NUBIVlab/SpiderCam/fpga/tb/components/drivers/FpDriver32.sv

import utilities_pkg::*;

class FpDriver32 #(type T, type I);

    TriggerableQueue #(T) in_queue;
    I inf;

    function new(
        TriggerableQueue #(T) in_queue,
        I inf
    );
        this.in_queue = in_queue;
        this.inf = inf;
    endfunction

    task automatic drive_fp(T floating_points);
        inf.fp_a_i  <= floating_points.a;
        inf.fp_b_i  <= floating_points.b;
        inf.valid_i <= 1;
        @(posedge this.inf.clk_i);
    endtask;

    task automatic invalidate();
        inf.valid_i <= 0;
    endtask;

    task automatic run();
        T floating_points;
        invalidate();

        forever begin
            in_queue.pop(floating_points);
            drive_fp(floating_points);
            invalidate();
        end
    endtask
endclass
