NUBIVlab/SpiderCam/fpga/projects/dfdd/custom_box_h_3_uint8_to_uint10.sv

module custom_box_h_3_uint8_to_uint10 (
    input clk_i,
    input rst_i,

    input [7:0]  window_i [1][3],
    input [15:0] col_i,
    input [15:0] row_i,
    input        valid_i,

    output [9:0] data_o,
    output [15:0] col_o,
    output [15:0] row_o,
    output        valid_o

);

    logic [7:0]  window [1][3];
    logic [15:0] col;
    logic [15:0] row;
    logic        valid;

    always@(posedge clk_i) begin
        window <= window_i;
        col    <= col_i;
        row    <= row_i;
        if(rst_i) begin
            valid <= 0;
        end else begin
            valid <= valid_i;
        end
    end

    logic [8:0]  level_0 [2];
    logic [9:0]  level_1; 

    always_comb begin
        level_0[0] = window[0][0] + window[0][1];
        level_0[1] = {1'b0, window[0][2]};

        level_1 = level_0[0] + level_0[1];
    end

    assign data_o  = level_1;
    assign col_o   = col;
    assign row_o   = row;
    assign valid_o = valid;

endmodule
