NUBIVlab/SpiderCam/fpga/projects/dfdd/custom_burt_h_sint14_to_sint18.sv

module custom_burt_h_sint14_to_sint18 (
    input clk_i,
    input rst_i,

    input [13:0] window_i [1][5],
    input [15:0] col_i,
    input [15:0] row_i,
    input valid_i,

    output [17:0] data_o,
    output [15:0] col_o,
    output [15:0] row_o,
    output valid_o
);


    logic signed [13:0] window [1][5];
    logic        [15:0] col;
    logic        [15:0] row;
    logic               valid;

    always@(posedge clk_i) begin
        for(int c = 0; c < 5; c++) begin
            window[0][c] <= window_i[0][c];
        end
        col    <= col_i;
        row    <= row_i;
        if(rst_i) begin
            valid <= 0;
        end else begin
            valid <= valid_i;
        end
    end

    logic signed [16:0] mult_level [5];

    logic [17:0] level_0 [3];
    logic [18:0] level_1 [2];
    logic [19:0] level_2;

    always_comb begin
        mult_level[0] = window[0][0];          // * 1
        mult_level[1] = window[0][1] << 2;     // * 4 ( << preserves sign)
        mult_level[2] = window[0][2] * 6;      // * 6 ( 3'b110 is unsigned and from quick
        mult_level[3] = window[0][3] << 2;     //       testing on eda playground, does not
        mult_level[4] = window[0][4];          //       preserve sign for some reason. '6' is signed number)

        level_0[0] = mult_level[0] + mult_level[1];
        level_0[1] = mult_level[2] + mult_level[3];
        level_0[2] = {mult_level[4][16], mult_level[4]};

        level_1[0] = level_0[0] + level_0[1];
        level_1[1] = {level_0[2][16], level_0[2]};

        level_2 = level_1[0] + level_1[1];
    end

    assign data_o  = level_2[17:0];
    assign col_o   = col;
    assign row_o   = row;
    assign valid_o = valid;


endmodule
