NUBIVlab/SpiderCam/fpga/projects/dfdd/custom_burt_v_sint18_to_sint22.sv

module custom_burt_v_sint18_to_sint22 (
    input clk_i,
    input rst_i,

    input [17:0] window_i [5][1],
    input [15:0] col_i,
    input [15:0] row_i,
    input valid_i,

    output [21:0] data_o,
    output [15:0] col_o,
    output [15:0] row_o,
    output valid_o
);


    logic signed [17:0] window [5][1];
    logic        [15:0] col;
    logic        [15:0] row;
    logic               valid;

    always@(posedge clk_i) begin
        for(int r = 0; r < 5; r++) begin
            window[r][0] <= window_i[r][0];
        end
        col    <= col_i;
        row    <= row_i;
        if(rst_i) begin
            valid <= 0;
        end else begin
            valid <= valid_i;
        end
    end

    logic signed [20:0] mult_level [5];

    logic [21:0] level_0 [3];
    logic [22:0] level_1 [2];
    logic [23:0] level_2;

    always_comb begin
        mult_level[0] = window[0][0];          // * 1
        mult_level[1] = window[1][0] << 2;     // * 4
        mult_level[2] = window[2][0] * 6;      // * 6
        mult_level[3] = window[3][0] << 2;
        mult_level[4] = window[4][0];

        level_0[0] = mult_level[0] + mult_level[1];
        level_0[1] = mult_level[2] + mult_level[3];
        level_0[2] = {mult_level[4][20], mult_level[4]};

        level_1[0] = level_0[0] + level_0[1];
        level_1[1] = {level_0[2][21], level_0[2]};

        level_2 = level_1[0] + level_1[1];
    end

    assign data_o  = level_2[21:0];
    assign col_o   = col;
    assign row_o   = row;
    assign valid_o = valid;


endmodule
