NUBIVlab/SpiderCam/fpga/tb/components/monitors/FpMonitor32.sv

import utilities_pkg::*;

class FpMonitor32 #(type T, type I);
    localparam FP_WIDTH_REG = 32;
    TriggerableQueueBroadcaster #(T) out_broadcaster;
    I inf;

    function new(TriggerableQueueBroadcaster #(T) out_broadcaster,
                 I inf);
        this.out_broadcaster = out_broadcaster;
        this.inf = inf;
    endfunction

    task automatic run();
        T floating_points;
        forever begin
            @(negedge inf.clk_i);
            if(inf.valid_o) begin
                floating_points = new(0, 0, inf.fp_o);
                out_broadcaster.push(floating_points);
            end
        end
    endtask

endclass
